dilshan/limit-switch-alarm/siren-controller/siren-controller.kicad_sch

## KiCad design siren-controller/siren-controller.kicad_sch (2024-10-11)

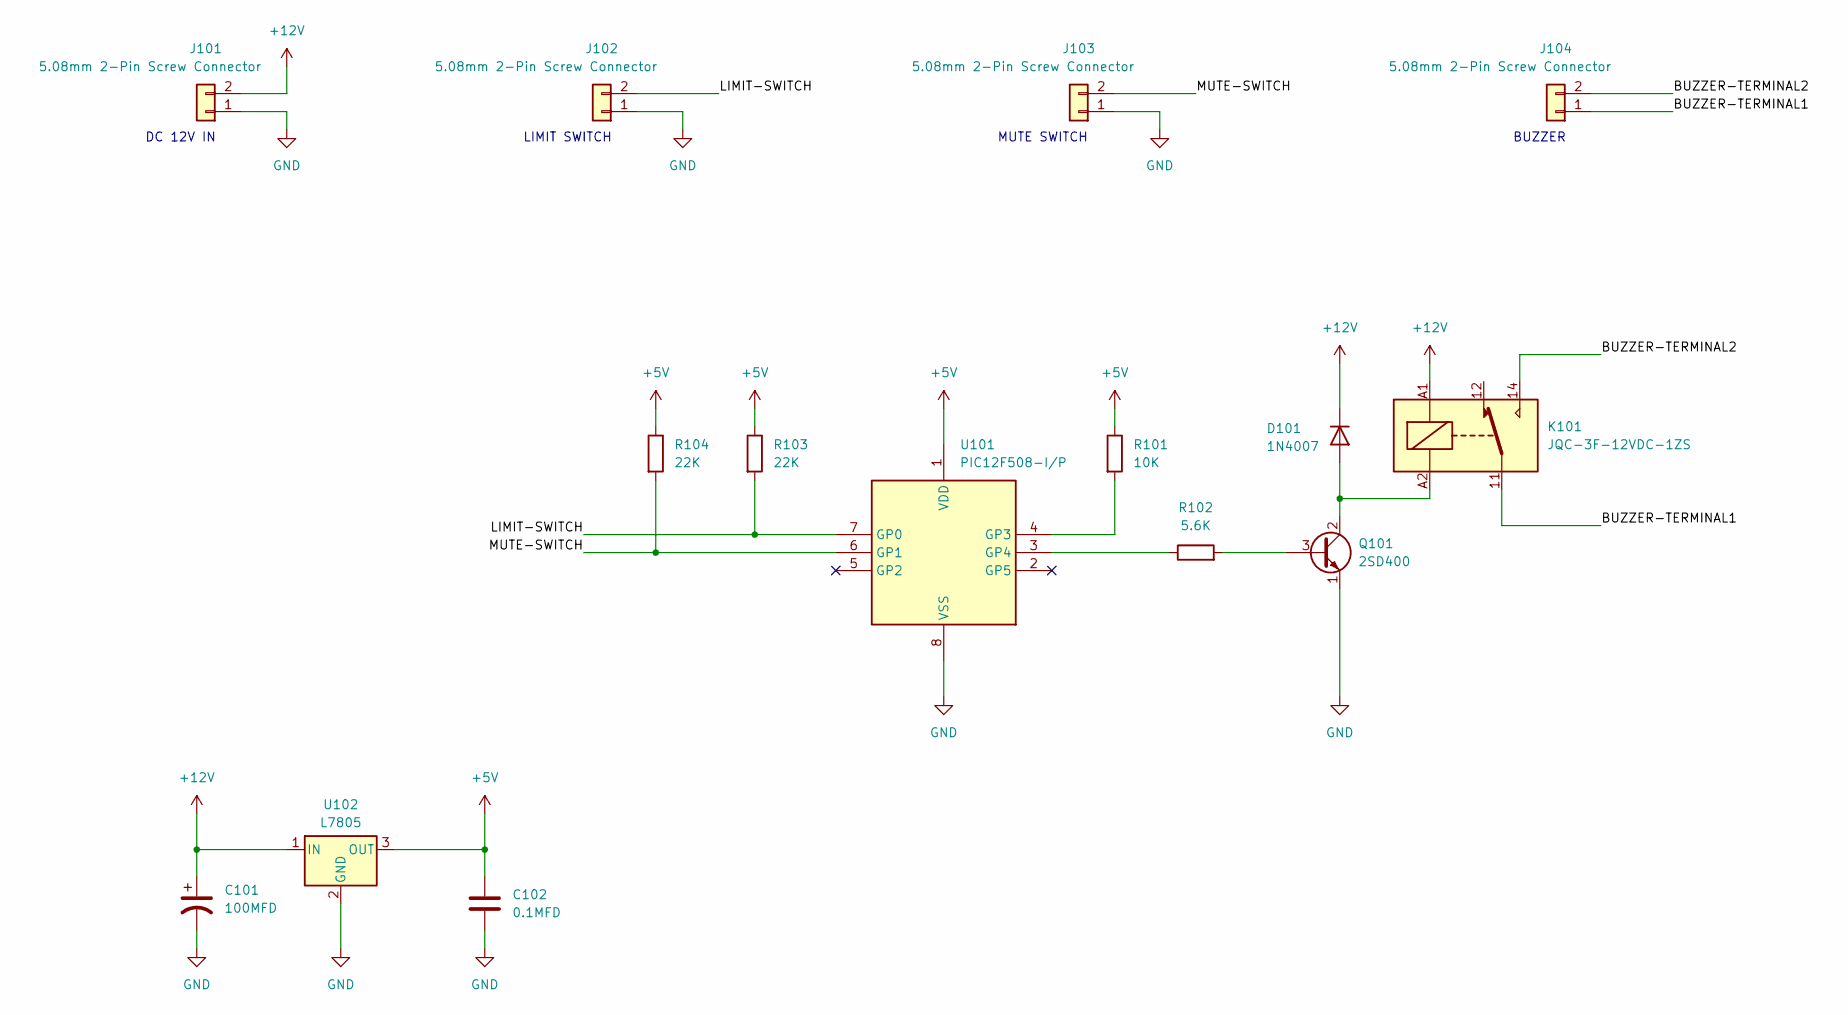
[picture p4: schematic siren-controller.kicad_sch]

Parts:
C101: 100MFD
C102: 0.1MFD
D101: 1N4007; D_DO-41_SOD81_P10.16mm_Horizontal
J101, J102, J103, J104: 5.08mm 2-Pin Screw Connector
K101: JQC-3F-12VDC-1ZS
Q101: 2SD400
R101: 10K
R102: 5.6K
R103, R104: 22K
U101: PIC12F508-I/P; DIP-8_W7.62mm
U102: L7805

Connections:
+5V: C102.1, R101.1, R103.1, R104.1, U101.1 (VDD), U102.3 (OUT)
+12V: C101.1, D101.1 (K), J101.2, K101.A1, U102.1 (IN)
BUZZER-TERMINAL1: J104.1, K101.11
BUZZER-TERMINAL2: J104.2, K101.14
GND: C101.2, C102.2, J101.1, J102.1, J103.1, Q101.1 (E), U101.8 (VSS), U102.2 (GND)
LIMIT-SWITCH: J102.2, R103.2, U101.7 (GP0)
MUTE-SWITCH: J103.2, R104.2, U101.6 (GP1)
unnamed: D101.2 (A), K101.A2, Q101.2 (C)
unnamed: Q101.3 (B), R102.2
unnamed: R101.2, U101.4 (GP3)
unnamed: R102.1, U101.3 (GP4)

Notes on the sheet:
DC 12V IN
MUTE SWITCH
BUZZER
LIMIT SWITCH
